lucaji/OpenTheremin4-MatrixUI/display-board-schematic/OT4-HT-display-board/Electronics-OT-HD.kicad_sch

## KiCad design display-board-schematic/OT4-HT-display-board/Electronics-OT-HD.kicad_sch (2025-08-11)

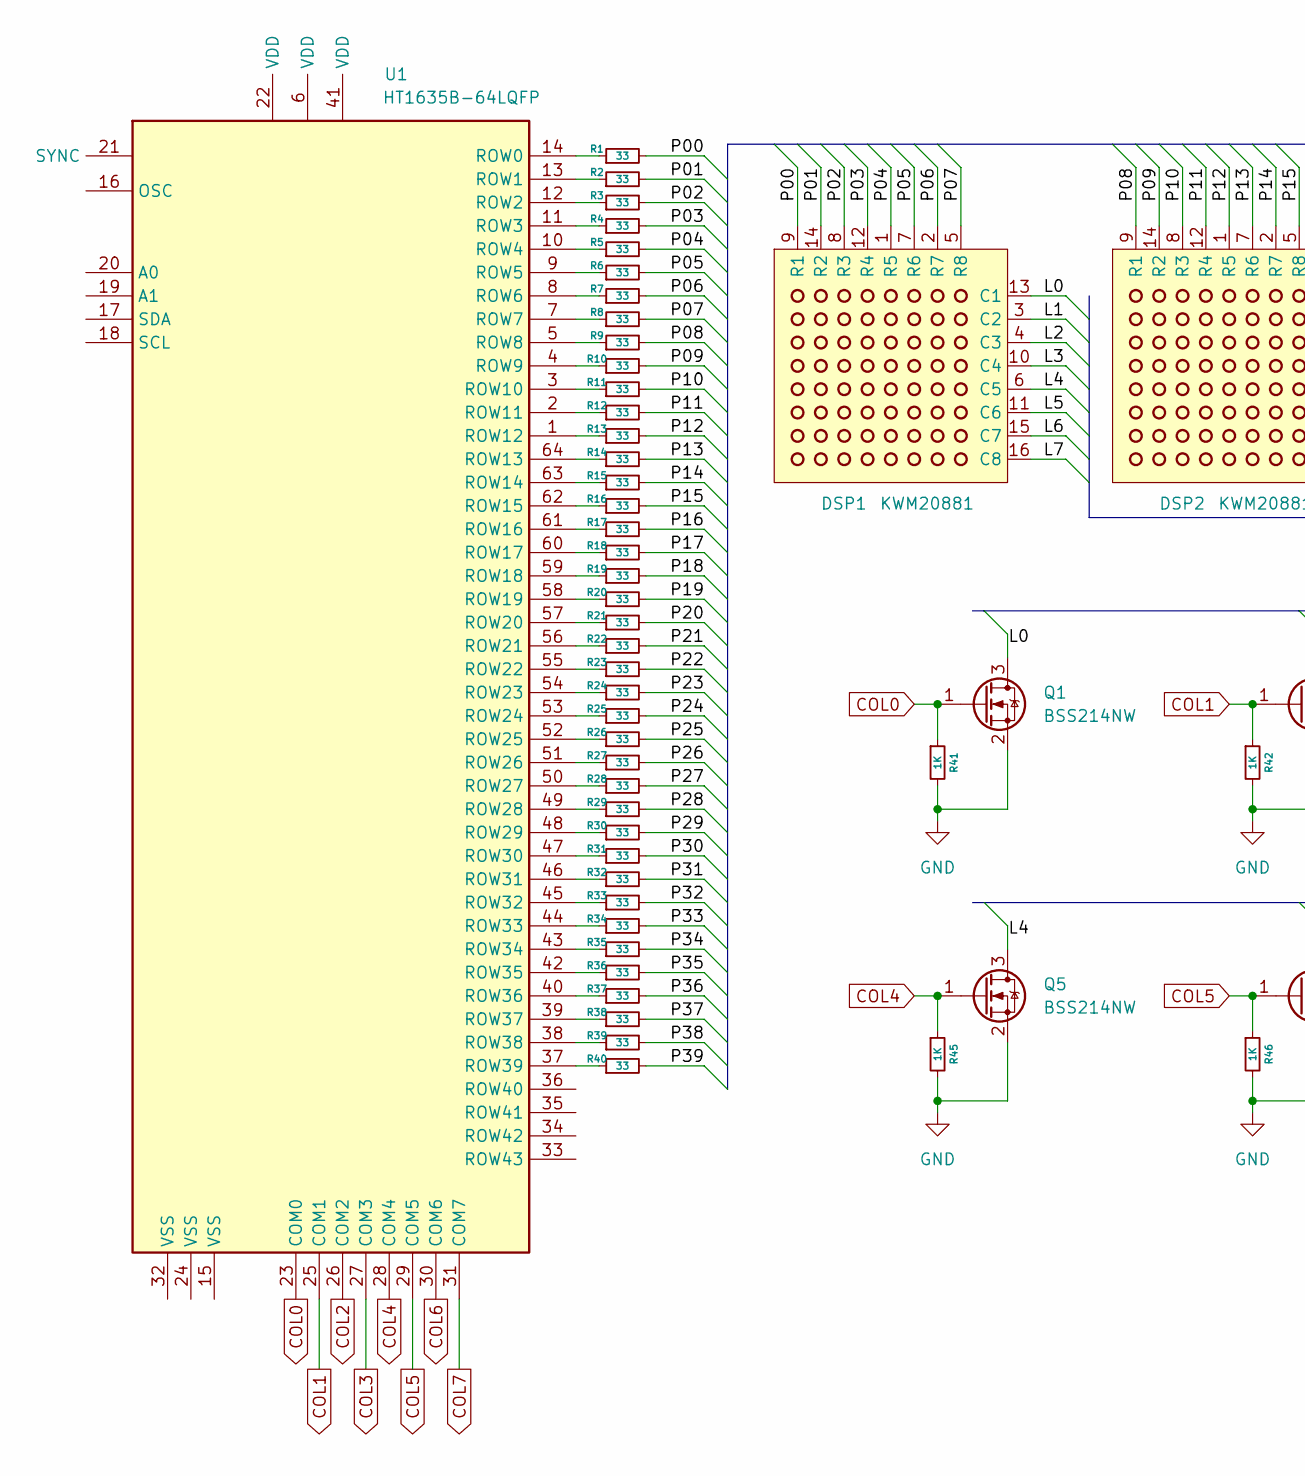
[picture p7: schematic Electronics-OT-HD.kicad_sch, part in row 1, column 1]

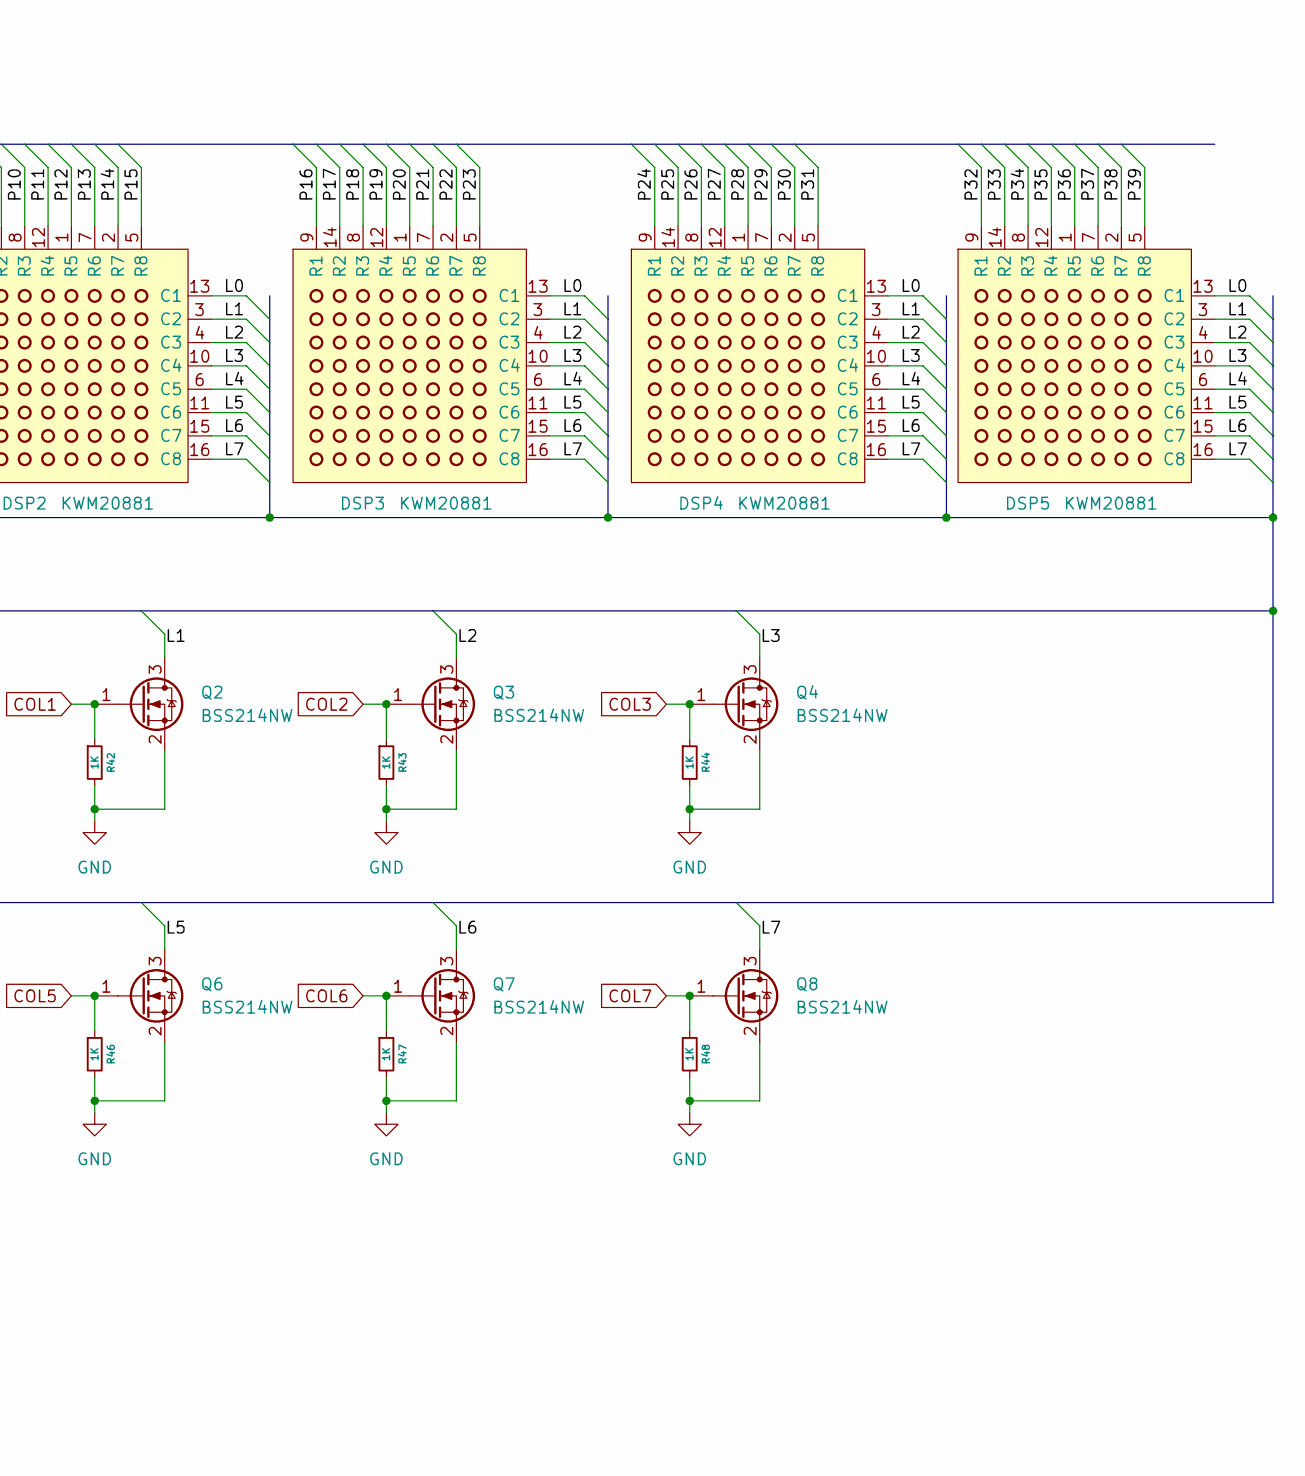
[picture p8: schematic Electronics-OT-HD.kicad_sch, part in row 1, column 2]

Parts:
DSP1, DSP2, DSP3, DSP4, DSP5: KWM20881
Q1, Q2, Q3, Q4, Q5, Q6, Q7, Q8: BSS214NW; SOT-323_SC-70
R1, R2, R3, R4, R5, R6, R7, R8, R9, R10, R11, R12, R13, R14, R15, R16, R17, R18, R19, R20, R21, R22, R23, R24, R25, R26, R27, R28, R29, R30, R31, R32, R33, R34, R35, R36, R37, R38, R39, R40: 33
R41, R42, R43, R44, R45, R46, R47, R48: 1K
U1: HT1635B-64LQFP; LQFP-64_7x7mm_P0.4mm

Connections:
COL0: Q1.1 (G), R41.1, U1.23 (COM0)
COL1: Q2.1 (G), R42.1, U1.25 (COM1)
COL2: Q3.1 (G), R43.1, U1.26 (COM2)
COL3: Q4.1 (G), R44.1, U1.27 (COM3)
COL4: Q5.1 (G), R45.1, U1.28 (COM4)
COL5: Q6.1 (G), R46.1, U1.29 (COM5)
COL6: Q7.1 (G), R47.1, U1.30 (COM6)
COL7: Q8.1 (G), R48.1, U1.31 (COM7)
GND: Q1.2 (S), Q2.2 (S), Q3.2 (S), Q4.2 (S), Q5.2 (S), Q6.2 (S), Q7.2 (S), Q8.2 (S), R41.2, R42.2, R43.2, R44.2, R45.2, R46.2, R47.2, R48.2
L0: DSP1.13 (C1), DSP2.13 (C1), DSP3.13 (C1), DSP4.13 (C1), DSP5.13 (C1), Q1.3 (D)
L1: DSP1.3 (C2), DSP2.3 (C2), DSP3.3 (C2), DSP4.3 (C2), DSP5.3 (C2), Q2.3 (D)
L2: DSP1.4 (C3), DSP2.4 (C3), DSP3.4 (C3), DSP4.4 (C3), DSP5.4 (C3), Q3.3 (D)
L3: DSP1.10 (C4), DSP2.10 (C4), DSP3.10 (C4), DSP4.10 (C4), DSP5.10 (C4), Q4.3 (D)
L4: DSP1.6 (C5), DSP2.6 (C5), DSP3.6 (C5), DSP4.6 (C5), DSP5.6 (C5), Q5.3 (D)
L5: DSP1.11 (C6), DSP2.11 (C6), DSP3.11 (C6), DSP4.11 (C6), DSP5.11 (C6), Q6.3 (D)
L6: DSP1.15 (C7), DSP2.15 (C7), DSP3.15 (C7), DSP4.15 (C7), DSP5.15 (C7), Q7.3 (D)
L7: DSP1.16 (C8), DSP2.16 (C8), DSP3.16 (C8), DSP4.16 (C8), DSP5.16 (C8), Q8.3 (D)
unnamed: R1.1, U1.14 (ROW0)
unnamed: R2.1, U1.13 (ROW1)
unnamed: R3.1, U1.12 (ROW2)
unnamed: R4.1, U1.11 (ROW3)
unnamed: R5.1, U1.10 (ROW4)
unnamed: R6.1, U1.9 (ROW5)
unnamed: R7.1, U1.8 (ROW6)
unnamed: R8.1, U1.7 (ROW7)
unnamed: R9.1, U1.5 (ROW8)
unnamed: R10.1, U1.4 (ROW9)
unnamed: R11.1, U1.3 (ROW10)
unnamed: R12.1, U1.2 (ROW11)
unnamed: R13.1, U1.1 (ROW12)
unnamed: R14.1, U1.64 (ROW13)
unnamed: R15.1, U1.63 (ROW14)
unnamed: R16.1, U1.62 (ROW15)
unnamed: R17.1, U1.61 (ROW16)
unnamed: R18.1, U1.60 (ROW17)
unnamed: R19.1, U1.59 (ROW18)
unnamed: R20.1, U1.58 (ROW19)
unnamed: R21.1, U1.57 (ROW20)
unnamed: R22.1, U1.56 (ROW21)
unnamed: R23.1, U1.55 (ROW22)
unnamed: R24.1, U1.54 (ROW23)
unnamed: R25.1, U1.53 (ROW24)
unnamed: R26.1, U1.52 (ROW25)
unnamed: R27.1, U1.51 (ROW26)
unnamed: R28.1, U1.50 (ROW27)
unnamed: R29.1, U1.49 (ROW28)
unnamed: R30.1, U1.48 (ROW29)
unnamed: R31.1, U1.47 (ROW30)
unnamed: R32.1, U1.46 (ROW31)
unnamed: R33.1, U1.45 (ROW32)
unnamed: R34.1, U1.44 (ROW33)
unnamed: R35.1, U1.43 (ROW34)
unnamed: R36.1, U1.42 (ROW35)
unnamed: R37.1, U1.40 (ROW36)
unnamed: R38.1, U1.39 (ROW37)
unnamed: R39.1, U1.38 (ROW38)
unnamed: R40.1, U1.37 (ROW39)
P00: DSP1.9 (R1), R1.2
P01: DSP1.14 (R2), R2.2
P02: DSP1.8 (R3), R3.2
P03: DSP1.12 (R4), R4.2
P04: DSP1.1 (R5), R5.2
P05: DSP1.7 (R6), R6.2
P06: DSP1.2 (R7), R7.2
P07: DSP1.5 (R8), R8.2
P08: DSP2.9 (R1), R9.2
P09: DSP2.14 (R2), R10.2
P10: DSP2.8 (R3), R11.2
P11: DSP2.12 (R4), R12.2
P12: DSP2.1 (R5), R13.2
P13: DSP2.7 (R6), R14.2
P14: DSP2.2 (R7), R15.2
P15: DSP2.5 (R8), R16.2
P16: DSP3.9 (R1), R17.2
P17: DSP3.14 (R2), R18.2
P18: DSP3.8 (R3), R19.2
P19: DSP3.12 (R4), R20.2
P20: DSP3.1 (R5), R21.2
P21: DSP3.7 (R6), R22.2
P22: DSP3.2 (R7), R23.2
P23: DSP3.5 (R8), R24.2
P24: DSP4.9 (R1), R25.2
P25: DSP4.14 (R2), R26.2
P26: DSP4.8 (R3), R27.2
P27: DSP4.12 (R4), R28.2
P28: DSP4.1 (R5), R29.2
P29: DSP4.7 (R6), R30.2
P30: DSP4.2 (R7), R31.2
P31: DSP4.5 (R8), R32.2
P32: DSP5.9 (R1), R33.2
P33: DSP5.14 (R2), R34.2
P34: DSP5.8 (R3), R35.2
P35: DSP5.12 (R4), R36.2
P36: DSP5.1 (R5), R37.2
P37: DSP5.7 (R6), R38.2
P38: DSP5.2 (R7), R39.2
P39: DSP5.5 (R8), R40.2
