lucaji/OpenTheremin4-MatrixUI/firmware/OT4-HT-display-firmware/src/bitmap_fonts.h

/**
 * @file bitmap_fonts.h
 * @brief character display bitmap
 * 
 * (c) 2025 Luca Cipressi (lucaji.github.io)
 * 
 * GNU GPL v3 or later.
 * 
 * REVISION HISTORY
 *         AUG 2025     Luca Cipressi (lucaji.githu.io) First commit
 * 
 */

#include <Arduino.h>


#ifndef _BITMAP_FONTS_H_
#define _BITMAP_FONTS_H_

const uint8_t Font_6x8[][8] PROGMEM = {
    { 0x00, 0x00, 0x00, 0x00, 0x00, 0x00, 0x00, 0x00 }, /* ' ' 0x20 */ 
    { 0x04, 0x04, 0x04, 0x04, 0x04, 0x00, 0x04, 0x00 }, /* '!' 0x21 */ 
    { 0x1B, 0x1B, 0x12, 0x00, 0x00, 0x00, 0x00, 0x00 }, /* '"' 0x22 */ 
    { 0x0A, 0x1F, 0x0A, 0x1F, 0x0A, 0x00, 0x00, 0x00 }, /* '#' 0x23 */ 
    { 0x08, 0x0E, 0x10, 0x0C, 0x02, 0x1C, 0x04, 0x00 }, /* '$' 0x24 */ 
    { 0x19, 0x19, 0x02, 0x04, 0x08, 0x13, 0x13, 0x00 }, /* '%' 0x25 */ 
    { 0x08, 0x14, 0x14, 0x08, 0x15, 0x12, 0x0D, 0x00 }, /* '&' 0x26 */ 
    { 0x0C, 0x0C, 0x08, 0x00, 0x00, 0x00, 0x00, 0x00 }, /* ''' 0x27 */ 
    { 0x04, 0x08, 0x08, 0x08, 0x08, 0x08, 0x04, 0x00 }, /* '(' 0x28 */ 
    { 0x08, 0x04, 0x04, 0x04, 0x04, 0x04, 0x08, 0x00 }, /* ')' 0x29 */ 
    { 0x0C, 0x12, 0x12, 0x0C, 0x00, 0x00, 0x00, 0x00 }, /* '*' 0x2A */ 
    { 0x00, 0x04, 0x04, 0x1F, 0x04, 0x04, 0x00, 0x00 }, /* '+' 0x2B */ 
    { 0x00, 0x00, 0x00, 0x00, 0x00, 0x0C, 0x0C, 0x08 }, /* ',' 0x2C */ 
    { 0x00, 0x00, 0x00, 0x0E, 0x00, 0x00, 0x00, 0x00 }, /* '-' 0x2D */ 
    { 0x00, 0x00, 0x00, 0x00, 0x00, 0x00, 0x10, 0x00 }, /* '.' 0x2E */ 
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
    0x00, 0x60, 0x90, 0x96, 0x95, 0x95, 0x66, 0x04, 
    0x00, 0x00, 0x00, 0x66, 0x55, 0x65, 0x35, 0x00, 
    0x00, 0x00, 0xE0, 0x59, 0x55, 0x59, 0x4D, 0x01, 
    0x00, 0x00, 0x00, 0x91, 0x5B, 0x55, 0x91, 0x00, 
    0x00, 0x00, 0x00, 0x65, 0x57, 0x65, 0x35, 0x00,
};

#endif // _BITMAP_FONTS_H_
