lucaji/OpenTheremin4-MatrixUI/firmware/OT4-HT-theremin-firmware/src/wavetable_0.h

/* Theremin WAVE Table - 1024 entries full table, amplitude -2048..2048*/

#include <avr/pgmspace.h>

const int16_t wavetable_0[1024] PROGMEM = {
-1,
13,
28,
42,
57,
71,
86,
100,
115,
129,
144,
159,
173,
188,
201,
216,
230,
245,
259,
273,
288,
302,
317,
330,
345,
358,
373,
387,
401,
416,
429,
444,
457,
472,
485,
500,
513,
527,
540,
555,
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
};
