lucaji/OpenTheremin4-MatrixUI/firmware/OT4-HT-theremin-firmware/src/calibration.cpp

#include "calibration.h"
#include "dac.h"
#include "timer.h"
#include "ihandlers.h"
#include "../../eeprom.h"
#include "../../build_options.h"
#include "hw.h"


// calibration
#define PITCH_FIXED_OSCILLATOR_FREQUENCY        500000      // XTAL1 = 16 MHz / 32 (Q5 of U2 - 4060D)
#define VOLUME_FIXED_OSCILLATOR_FREQUENCY       460800      // XTAL2 = 7.3728 MHz / 16 (Q4 of U3 - 4060D)
#define CALIBRATION_BASE_MAX_DRIFT              150         // maximum drift from target frequency for success calibration
const int16_t CalibrationTolerance = 15;
int32_t pitchCalibrationBase = 0;
const int16_t PitchFreqOffset = 700;
int32_t volCalibrationBase = 0;
const int16_t VolumeFreqOffset = 700;
const uint32_t master_clock_frequency = 16000000;

#ifdef SERIAL_DEBUG_MESSAGES
void printCalibrationDetails() {
    float pitchBeatHz = master_clock_frequency / pitchCalibrationBase;
    float volBeatHz = master_clock_frequency / volCalibrationBase;

    float voPitchFreq = PITCH_FIXED_OSCILLATOR_FREQUENCY - pitchBeatHz;
    float voVolFreq = VOLUME_FIXED_OSCILLATOR_FREQUENCY - volBeatHz;

    int16_t pitchDAC = 0;
    int16_t volumeDAC = 0;
    EEPROM.get(EEPROM_PITCH_DAC_VOLTAGE_ADDRESS, pitchDAC);
    EEPROM.get(EEPROM_VOLUME_DAC_VOLTAGE_ADDRESS, volumeDAC);

    Serial.println(F("--- Calibration Summary ---"));
    Serial.print(F("Pitch ticks:        ")); Serial.println(pitchCalibrationBase);
    Serial.print(F("Pitch beat freq:    ")); Serial.print(pitchBeatHz, 2); Serial.println(F(" Hz"));
    Serial.print(F("VO_PITCH freq:    ")); Serial.print(voPitchFreq, 2); Serial.print(F(" Hz (vs ")); Serial.print(PITCH_FIXED_OSCILLATOR_FREQUENCY - PitchFreqOffset); Serial.println(F(" Hz target)"));
    DEBUG_PRINT(F("P_DAC="));DEBUG_PRINTLN(pitchDAC);

    Serial.println();

    Serial.print(F("Volume ticks:     ")); Serial.println(volCalibrationBase);
    Serial.print(F("Volume beat freq: ")); Serial.print(volBeatHz, 2); Serial.println(F(" Hz"));
    Serial.print(F("VO_VOL freq:        ")); Serial.print(voVolFreq, 2); Serial.print(F(" Hz (vs ")); Serial.print(VOLUME_FIXED_OSCILLATOR_FREQUENCY - VolumeFreqOffset); Serial.println(F(" Hz target)"));
    DEBUG_PRINT(F("V_DAC="));DEBUG_PRINTLN(volumeDAC);

    Serial.println(F("---------------------------"));
}
#endif


/*******************************************
 *          CALIBRATION ROUTINES
 *******************************************/

 
/**
 * @brief Measures the absolute frequency of the pitch oscillator (VO_PITCH).
 *
 * This function uses Timer1 in normal mode to count the number of clock cycles
 * over a 1-second window (via `delay(1000)`) to compute the frequency of the
 * signal arriving on PD5 (ICP1).
 *
 * Timer1 is configured with a prescaler of 1024, so its effective counting frequency is:
 *   16,000,000 / 1024 = 15,625 Hz.
 *
 * The function resets the counter and overflow register before starting measurement,
 * then accumulates the total number of clock ticks over the 1-second duration.
 *
 * @details
 * - This method is typically called during the calibration procedure.
 * - It indirectly measures VO_PITCH, a ~500 kHz RF signal, by leveraging
 *   frequency aliasing from the physical RF circuitry and flip-flop gating (F_PITCH).
 * - Timer1 overflows at 65536 ticks, so the `timer_overflow_counter` accounts for overflows.
 *
 * The final frequency count is:
 * @code
 *   frequency = TCNT1 + 65536 * timer_overflow_counter;
 * @endcode
 *
 *
 * @return The measured pitch frequency in Timer1 ticks over 1 second, to be converted externally.
 */
uint32_t GetPitchMeasurement() {
    DEBUG_PRINT(F("GetPitchMeasurement "));
    TCNT1 = 0;                      // Reset Timer1 counter
    timer_overflow_counter = 0;     // Reset overflow counter
    // Set Timer1 with prescaler 1024 (CS12 | CS11 | CS10)
    // Resulting timer tick: 16 MHz / 1024 = 15.625 kHz
    TCCR1B = (1 << CS12) | (1 << CS11) | (1 << CS10);
    delay(1000);                    // Measure duration: 1000 ms (blocking)
    TCCR1B = 0;                     // Stop Timer1 after measurement
    // Combine Timer1 count with overflow count to get full frequency count
    uint32_t frequency = TCNT1;
    uint32_t temp = 65536UL * (uint32_t)timer_overflow_counter;
    frequency += temp;
    // measured_Hz = measuredTicks * (16e6 / 1024) / 1.0 for 1s integration time
    DEBUG_PRINT(F("tcnt1="));DEBUG_PRINT(TCNT1);DEBUG_PRINT(F(" ovfl="));DEBUG_PRINT(timer_overflow_counter);DEBUG_PRINT(F(" f="));DEBUG_PRINTLN(frequency);
    return frequency;
}

/**
 * @brief Measures the frequency of the volume antenna oscillator (VO_VOL).
 *
 * This function uses Timer/Counter0 in external clock mode to count rising edges
 * from the VO_VOL signal (connected to T0 / PD4 / Digital Pin 4) over a 1-second
 * gate window determined by Timer1 overflow.
 *
 * Timer1 is preloaded with 49911 to overflow after ~1 second (65536 - 49911 = 15625 ticks @ 16 MHz).
 * Timer0 counts external rising edges from VO_VOL during this gate time.
 * The result is the total number of VO_VOL cycles within one second.
 *
 * @return Frequency in Hz as an uint32_t value.
 *
 * @note Timer0 is 8-bit, so an overflow counter is used to extend its range.
 *       This approach trades resolution for simplicity, which is acceptable for volume
 *       since it does not require the same precision or update rate as pitch.
 *
 * @warning This method assumes Timer0 and Timer1 are not used elsewhere during execution.
 */
uint32_t GetVolumeMeasurement() {
    DEBUG_PRINT(F("GetVolumeMeasurement "));
    timer_overflow_counter = 0;                                 // Clear overflow tracker for Timer0
    TCNT0 = 0;                                                  // Reset Timer0 (pulse counter)
    TCNT1 = 49911;                                              // Preload Timer1 so it overflows in 1s (65536 - 49911 = 15625 ticks @ 16 MHz)
    // Set Timer0 to external clock on T0 (PD4), count on rising edge
    TCCR0B = (1 << CS02) | (1 << CS01) | (1 << CS00);
    // Clear Timer1 overflow flag (to detect overflow event)
    TIFR1 = (1 << TOV1);                                        //Timer1 INT Flag Reg: Clear Timer Overflow Flag
    while (!(TIFR1 & ((1 << TOV1)))) {}                         // Wait until Timer1 overflows (1s interval)
    TCCR0B = 0;                                                 // Stop TimerCounter 0
    uint32_t frequency = TCNT0;                                 // Retrieve measured pulse count from Timer0 and overflow counter
    uint32_t temp = (uint32_t)timer_overflow_counter;           // Each Timer0 overflow = 256 pulses
    frequency += temp * 256;
    DEBUG_PRINT(F("tcnt0="));DEBUG_PRINT(TCNT0);DEBUG_PRINT(F(" ovfl="));DEBUG_PRINT(temp);DEBUG_PRINT(F(" f="));DEBUG_PRINTLN(frequency);
    return frequency;
}

/**
 * @brief Completes the automatic calibration routine for pitch and volume oscillators.
 *
 * This function captures reference frequency measurements from both VO_PITCH and VO_VOL,
 * storing baseline counter values and computing calibration constants used during runtime
 * for frequency-to-pitch/volume translation. The results are saved into EEPROM for persistence.
 *
 * ### Calibration Steps:
 * 1. **Pitch:**
 *    - Resets internal pitch flags and timers.
 *    - Waits for a valid `pitchValueAvailable` flag, or times out after 10 ms.
 *    - Captures the base pitch period and computes:
 *      - `pitchCalibrationBase`: raw Timer1 delta
 *
 * 2. **Volume:**
 *    - Same logic as pitch, using `volValueAvailable` and `vol_counter`.
 *    - Captures `volCalibrationBase` from the Timer1 delta.
 *
 * 3. **EEPROM Storage:**
 *    - Stores calibration values:
 *      - At address 4: `pitchCalibrationBase` (4 bytes)
 *      - At address 8: `volCalibrationBase` (4 bytes)
 *
 * @returns true if success, to avoid writing invalid calibration data in EEPROM
 *
 * @note Calibration uses blocking wait with optional timeout of 10 ms for each channel.
 *       It assumes the player is holding still, and RF conditions are stable.
 *
 * @warning Requires successful pitch/volume ISR processing to populate
 *          `pitchValueAvailable` and `volumeValueAvailable` before timeout.
 *
 * @see GetPitchMeasurement()
 * @see GetVolumeMeasurement()
 */
bool calibration_finalize() {
    // use temporary storage in case calibration fails
    // so to store only in case both have success
    // avoid partial calibration changes
    int32_t pitch_calibration_val = 0;
    int32_t volume_calibration_val = 0;
    bool success = false;

    // --- Final Pitch calibration persistance ---
    pitchValueAvailable = false;   //< Clear pitchValueAvailable
    resetTimer();       // Reset system timer
    pitch_counter_l = pitch_counter; // Store previous pitch counter value

    // Wait for new pitch value or timeout after 10ms
    while (!success && !timerExpiredMillis(10)) { success = pitchValueAvailable; }
    if (success) {
        success = false; // retry for volume
        pitch_calibration_val = pitch;           // Store raw pitch counter
        // --- Final Volume calibration persistance---
        volumeValueAvailable = false;     // Clear volumeValueAvailable
        resetTimer();       // Reset system timer
        vol_counter_l = vol_counter;   // Store previous volume counter value
        // Wait for new volume value or timeout after 10ms
        while (!success && !timerExpiredMillis(10)) { success = volumeValueAvailable; }
        if (success) {
            volume_calibration_val = vol;               // Store raw volume counter
            #ifdef SERIAL_DEBUG_MESSAGES
            printCalibrationDetails();
            #endif

            // check if calibration was within valid limits
            float pitchBeatHz = master_clock_frequency / pitchCalibrationBase;
            float volBeatHz = master_clock_frequency / volCalibrationBase;
            success = abs(pitchBeatHz - PitchFreqOffset) < CALIBRATION_BASE_MAX_DRIFT;
            if (success) {
                success = abs(volBeatHz - VolumeFreqOffset) < CALIBRATION_BASE_MAX_DRIFT;
                if (success) {
                    pitchCalibrationBase = pitch_calibration_val;
                    volCalibrationBase = volume_calibration_val;
                    // --- Store calibration baseline results in EEPROM ---
                    EEPROM.put(EEPROM_PITCH_DAC_CALIBRATION_BASE_ADDRESS, pitchCalibrationBase);    // Save pitch baseline (4 bytes)
                    EEPROM.put(EEPROM_VOLUME_DAC_CALIBRATION_BASE_ADDRESS, volCalibrationBase);     // Save volume baseline (4 bytes)
                }
            }
        }
    }
    return success;
}

/**
 * @brief Performs pitch oscillator calibration using a numerical approximation.
 *
 * This function tunes the DAC output controlling the VO_PITCH oscillator to align
 * the oscillator frequency with the reference frequency derived from the 16 MHz crystal.
 *
 * ### Calibration Goal:
 * - Find the correct DAC setting (`pitchXn`) so that the pitch oscillator outputs exactly 500 kHz,
 *   matching the divided reference frequency (U2 Q5 = 16 MHz / 32).
 *
 * ### Algorithm Summary:
 * - The search interval is initialized with `pitchXn0 = 0` and `pitchXn1 = 4095`.
 * - It uses a form of secant method (similar to dichotomy/bisection) to iteratively find
 *   the optimal DAC value that minimizes the frequency delta (`pitchfn0 - pitchfn1`).
 * - Loop is limited to 12 iterations, sufficient for 12-bit resolution convergence.
 *
 * ### EEPROM Storage:
 * - The final calibrated DAC value is written to EEPROM address 0.
 * 
 * @returns true if successfully calibrated.
 *
 * @warning Requires VO_PITCH oscillator to be stable during calibration.
 * @note Uses blocking `delay()` and relies on GetPitchMeasurement(), which uses Timer1 counting.
 * @see GetQMeasurement()
 * @see GetPitchMeasurement()
 */
bool calibrate_pitch() {
    int16_t pitchXn0 = 0;    // Lower DAC bound
    int16_t pitchXn1 = DAC_12BIT_MAX;    // Upper DAC bound (max for 12-bit DAC)
    int16_t pitchXn2 = 0;    // Midpoint in iteration
    static const float q0 = (master_clock_frequency / master_clock_frequency * PITCH_FIXED_OSCILLATOR_FREQUENCY); // Count Timer1 ticks over 31.25k cycles
    long pitchfn0 = 0;       // Measured pitch frequencies
    long pitchfn1 = 0;
    long pitchfn = q0 - PitchFreqOffset;     // Correct for calibration drift

    DEBUG_PRINTLN(F("\nPITCH CALIBRATION"));
    DEBUG_PRINT(F("Set f= ")); DEBUG_PRINTLN(pitchfn);

    ihInitialisePitchMeasurement();     // Setup Timer1 and associated ISR flags
    //sei();
    SPImcpDACinit();                    // Initialize DACs

    SPImcpDAC2Bsend(1600);          // bias the volume oscillator for pitch calibration
    SPImcpDAC2Asend(pitchXn0);      // Frequency at low DAC value
    delay(100);
    pitchfn0 = GetPitchMeasurement();
    SPImcpDAC2Asend(pitchXn1);      // Frequency at high DAC value
    delay(100);
    pitchfn1 = GetPitchMeasurement();

    DEBUG_PRINT(F("Tune range ")); DEBUG_PRINT(pitchfn0); DEBUG_PRINT(F(" to ")); DEBUG_PRINTLN(pitchfn1);

    uint8_t cal_iteration = 0; // Max 12 iterations
    while (abs(pitchfn0 - pitchfn1) > CalibrationTolerance && (cal_iteration < 12)) {
        SPImcpDAC2Asend(pitchXn0);
        delay(100);
        pitchfn0 = GetPitchMeasurement() - pitchfn;

        SPImcpDAC2Asend(pitchXn1);
        delay(100);
        pitchfn1 = GetPitchMeasurement() - pitchfn;

        // Secant approximation to refine DAC value
        pitchXn2 = pitchXn1 - ((pitchXn1 - pitchXn0) * pitchfn1) / (pitchfn1 - pitchfn0); // new DAC value

        DEBUG_PRINT("\nDAC L: "); DEBUG_PRINT(pitchXn0); DEBUG_PRINT(" fL: "); DEBUG_PRINTLN(pitchfn0);
        DEBUG_PRINT("DAC H: "); DEBUG_PRINT(pitchXn1); DEBUG_PRINT(" fH: "); DEBUG_PRINTLN(pitchfn1);

        pitchXn0 = pitchXn1;
        pitchXn1 = pitchXn2;

        HW_LED_BLUE_TOGGLE;     // visual feedback
        cal_iteration++;
    }
    delay(100);

    bool success = cal_iteration < 12;
    if (success) {
        EEPROM.put(EEPROM_PITCH_DAC_VOLTAGE_ADDRESS, pitchXn0); // Store final calibrated DAC value for VO_PITCH
    }
    return success;
}

/**
 * @brief Replacement function for delay() used only during VO_VOL measurement in calibration.
 *
 * calling delay() will block the MCU completely because the same timer
 * used by delay() is already being used for the actual frequency measurement.
 * The fixed constant 44316 represents the equivalent of 100ms of delay.
 *
 * @warning Requires stable oscillator and clean signal edges on VO_VOL for accurate timing.
 * 
 */
void delay_NOP() {
    volatile unsigned long i = 0;
    for (i = 0; i < 44316; i++) {
        __asm__ __volatile__("nop");
    }
}


/**
 * @brief Performs volume oscillator calibration using iterative frequency measurement.
 *
 * This function finds the optimal DAC value that aligns the VO_VOL oscillator frequency
 * with the reference frequency derived from the second crystal (X2 at 7.3728 MHz).
 *
 * ### Calibration Goal:
 * - Align the VO_VOL oscillator frequency with a nominal target:  
 *   7.3728 MHz / 16 (Q4 from U2) = 460,800 Hz.
 *
 * ### Calibration Strategy:
 * - Like the pitch routine, this uses a secant-like numerical approach over 12-bit DAC range.
 * - Uses a 100 ms delay (`waitNOP(44316)`) between DAC value changes and frequency measurement
 *   to ensure the RF circuit stabilizes.
 *
 * ### EEPROM Storage:
 * - The resulting DAC value is stored at EEPROM address 2.
 *
 * @returns true if successfully calibrated.
 * 
 * @note The DAC2B channel is used for volume oscillator control.
 * @warning Requires stable oscillator and clean signal edges on VO_VOL for accurate timing.
 * @see GetVolumeMeasurement()
 */
bool calibrate_volume() {
    int16_t volumeXn0 = 0;   // Lower DAC bound
    int16_t volumeXn1 = DAC_12BIT_MAX;   // Upper DAC bound
    int16_t volumeXn2 = 0;   // Next DAC trial value
    // Calculate actual frequency from X2 crystal via prior master_clock_frequency (from X1 at 16 MHz)
    // Target frequency: 7372800 / 16 = 460800
    static const float q0 = (master_clock_frequency / master_clock_frequency * VOLUME_FIXED_OSCILLATOR_FREQUENCY);            // Calculated oscillator frequency based on crystal measurement
    int32_t volumefn0 = 0;      // Frequency measurements
    int32_t volumefn1 = 0;
    int32_t volumefn = q0 - VolumeFreqOffset;

    DEBUG_PRINTLN(F("\nVOLUME CALIBRATION"));
    DEBUG_PRINT("Vf="); DEBUG_PRINTLN(volumefn);

    ihInitialiseVolumeMeasurement();    // Configure Timer0 and related registers
    //sei();
    SPImcpDACinit();                    // Re-initialize DAC interface

    // Measure low and high frequency extremes for DAC sweep range
    SPImcpDAC2Bsend(volumeXn0);
    delay_NOP(); 
    volumefn0 = GetVolumeMeasurement();
    SPImcpDAC2Bsend(volumeXn1);
    delay_NOP();
    volumefn1 = GetVolumeMeasurement();

    DEBUG_PRINT(F("Tune range ")); DEBUG_PRINT(volumefn0); DEBUG_PRINT(" to "); DEBUG_PRINTLN(volumefn1);

    uint8_t cal_iteration = 0; // Max 12 iterations
    while (abs(volumefn0 - volumefn1) > CalibrationTolerance && (cal_iteration < 12)) {
        SPImcpDAC2Bsend(volumeXn0);
        delay_NOP();
        volumefn0 = GetVolumeMeasurement() - volumefn;
        SPImcpDAC2Bsend(volumeXn1);
        delay_NOP();
        volumefn1 = GetVolumeMeasurement() - volumefn;
        // Secant method refinement
        volumeXn2 = volumeXn1 - ((volumeXn1 - volumeXn0) * volumefn1) / (volumefn1 - volumefn0); // calculate new DAC value

        DEBUG_PRINT("\nDAC L: "); DEBUG_PRINT(volumeXn0); DEBUG_PRINT(" fL: "); DEBUG_PRINTLN(volumefn0);
        DEBUG_PRINT("DAC H: "); DEBUG_PRINT(volumeXn1); DEBUG_PRINT(" fH: "); DEBUG_PRINTLN(volumefn1);

        volumeXn0 = volumeXn1;
        volumeXn1 = volumeXn2;

        HW_LED_BLUE_TOGGLE;     // visual feedback
        cal_iteration++;
    }
    bool success = cal_iteration < 12;
    if (success) {
        EEPROM.put(EEPROM_VOLUME_DAC_VOLTAGE_ADDRESS, volumeXn0); // Store DAC value for volume oscillator compensation
    }
    return success;
}

bool calibration_start() {    
    bool success = calibrate_pitch();
    if (success) {
        success = calibrate_volume();
    } else {
        // restore previous calibration DAC values if failed
        calibration_read();
    }

    ihInitialiseTimer();
    ihInitialiseInterrupts();
    millitimer(100);
    if (success) {
        success = calibration_finalize();
    }
    Serial.write(success?STATE_CMD_CALIBRATION_SUCCESS:STATE_CMD_CALIBRATION_ERROR);
    return success;
}


void calibration_read() {
    SPImcpDACinit();
    int16_t pitchDAC = 0;
    int16_t volumeDAC = 0;
    EEPROM.get(EEPROM_PITCH_DAC_VOLTAGE_ADDRESS, pitchDAC);
    EEPROM.get(EEPROM_VOLUME_DAC_VOLTAGE_ADDRESS, volumeDAC);
    EEPROM.get(EEPROM_PITCH_DAC_CALIBRATION_BASE_ADDRESS, pitchCalibrationBase);
    EEPROM.get(EEPROM_VOLUME_DAC_CALIBRATION_BASE_ADDRESS, volCalibrationBase);
    SPImcpDAC2Asend(pitchDAC);
    SPImcpDAC2Bsend(volumeDAC);
    
    #ifdef SERIAL_DEBUG_MESSAGES
    printCalibrationDetails();
    #endif

    // TODO: check if valid calibration
}
